LogiAI-Marmara/Grid-Up-Hackathon/modul-sim/README.md

# modul-sim — Sentetik Modül Veri Üreteci ve Modül Mantığı

Grid Up Hackathon — İZ A (Saha ve Veri Yolu) bileşeni.

Pano içine yerleştirilen izleme modülünün ölçüm döngüsünü, termal dizi matrisini,
sensör davranışını ve arıza mekanizmalarını sentetik olarak simüle eden CLI aracıdır.

---

## 1. Ne Üretir?

Modül simülatörü, panodaki donanımın üreteceği paketleri **Sözleşme ② (`modul_paketi.schema.json`)**
formatında üretir. Çıktı standart `stdout` akışına yazılır (ndjson veya json dizi), çalışma
istatistikleri ise `stderr`'e basılır:

- `modul_id`: `{saha}-{pano}-{modul}` hiyerarşik kimliği (örn. `TR041-P01-M1`)
- `zaman`: ISO 8601 UTC zaman damgası
- `olcumler`: `akim_l1`, `akim_l2`, `akim_l3`, `akim_notr`, `termal_maks`, `termal_ort` (her paket); `ortam_sicaklik`, `nem` (60 sn'de bir); `ark_olay` (olay olunca)
- `termal_ozet`: `maks`, `maks_konum`, `bolge_ort` (4 bölge)
- `termal_kare`: 32×24 = 768 elemanlı sıcaklık matrisi, her pakette (pakette 0,01 °C; toplama DB'de int16 0,1 °C)
- `modul_durum`: `besleme` (`sebeke`/`yedek`), `sinyal` (dBm), `yazilim_surumu`

---

## 2. Desteklenen 7 Arıza Senaryosu

Karar kaydı §7.6 ile tanımlı tüm arıza senaryoları simüle edilebilir:

| Senaryo Adı (`--senaryo`) | Belirti | Beklenen Anomali Tipi |
|---|---|---|
| `gevsek_klemens` | Akım sabitken tek noktada (klemens) aşırı ısınma | `sicak_nokta`, `akim_sicaklik_sapmasi` |
| `asiri_yuk` | Tüm faz akımları anma değerini aşar, genel pano sıcaklığı artar | `asiri_yuk`, `ortam_sicaklik_yuksek` |
| `faz_dengesizlik` | Fazlar arası akım farkı ve nötr akımı yükselir | `faz_dengesizligi` |
| `nem_yuksek` | Bağıl nem yükselir, çiğ noktasına yaklaşarak yoğuşma riski doğurur | `nem_yuksek` |
| `ark_olay` | Optik ark algılama kaydı (TVOC-2 Modbus trip sinyali) | `ark` |
| `sensor_ariza` | Sensör donması veya gürültülü okuma (`kalite: supheli/yok`) | `sensor_arizasi` |
| `modul_saglik` | Şebeke besleme kaybı (`yedek`), RF sinyal düşüşü, saat kayması | `modul_saglik` |

Senaryo listesini terminalden görüntülemek için:
```bash
python -m modul_sim --liste
```

---

## 3. Kurulum ve Çalıştırma

Repo kök dizininde veya `modul-sim/` dizininde:

```bash
# Bağımlılıkları yükleme
pip install -e modul-sim/

# Varsayılan normal çalışma (9 modül, 60 dk, ndjson)
python -m modul_sim

# Belirli bir arıza senaryosu ile üretim (ör. gevşek klemens)
python -m modul_sim --senaryo gevsek_klemens --modul 9 --sure 60 > veri.ndjson

# Toplama servisine doğrudan canlı borulama (pipeline)
python -m modul_sim --senaryo gevsek_klemens | while read -r paket; do
    curl -s -X POST http://localhost:8000/paket \
         -H "Content-Type: application/json" \
         -d "$paket"
done

# Sözleşme doğrulamasını zorunlu tutarak koşu
python -m modul_sim --dogrula --senaryo asiri_yuk
```

### Parametreler

- `--senaryo`: Arıza senaryosu seçimi (boş bırakılırsa normal sakin profil)
- `--modul N`: Simüle edilecek modül sayısı (Demo: 9, Yük testi: 100)
- `--sure DK`: Simülasyon penceresi uzunluğu (dakika)
- `--tohum N`: Rastgele sayı üreteci tohumu (deterministik tekrarlanabilirlik)
- `--baslangic ISO`: Simülasyon başlangıç zamanı (varsayılan: koşunun şu an bitmesini sağlayacak an)
- `--cikti`: `ndjson` (satır satır) veya `json` (tek dizi)
- `--dogrula`: Her paketi çıkışta `modul_paketi.schema.json` şemasına karşı doğrular
- `--senaryo-bas DK` / `--senaryo-sure DK`: senaryonun başlama anı ve rampa süresi (varsayılan: koşunun %35'inde başlar, %55'i boyunca tırmanır)
- `--senaryo-modul ID[,ID...]`: senaryoyu yalnız bu modüllere uygula, kalanlar temiz kalır
- `--senaryo-oran 0-1`: senaryoyu filonun bu kesrine uygula (tohumdan deterministik seçim), kalanlar temiz
- `--etiket PATH`: koşu bitince kör test **etiket dosyasını** yaz (İZ B formatı, `analiz/README.md` "Etiket dosyası formatı": `senaryolar[].baslangic / kritik_esik`, `temiz_moduller`, `kapsam`)
- `--sessiz`: stderr'e koşu özeti basma

### Kör test seti üretme

```bash
# 20 modül, 12 saat; modüllerin %30'unda gevşek klemens, kalan 14 modül temiz
python -m modul_sim --senaryo gevsek_klemens --modul 20 --sure 720 --senaryo-oran 0.3 --etiket etiket.json > kor.ndjson
```

Veri (`kor.ndjson`) veritabanına gider; `etiket.json` dedektör çıktısı dondurulana kadar üreticide kalır
(`analiz/README.md` "Kör test protokolü"). `kritik_esik` rampanın sonu, ark için ilk trip anı; etiketteki
senaryo adları İZ B sözlüğüyle (`faz_dengesizligi`, `nem_yukselmesi`, `ark_olayi`, `sensor_arizasi`) yazılır,
CLI adları değişmez.

---

## 4. Testler

```bash
pytest modul-sim/tests/
```

Tüm senaryoların veri üretimi, fizik motorunun ısı transferi kısıtları ve sözleşme uyumluluğu
otomatik testlerle doğrulanmaktadır.

İlgili tasarım dokümantasyonu: [`docs/track-a/07-yazilim-akis.md`](../docs/track-a/07-yazilim-akis.md)
