LogiAI-Marmara/Grid-Up-Hackathon/docs/track-a/07-yazilim-akis.md

# 7. Modül Yazılım Akış Diyagramı

**Teslimat karşılığı:** T3 (yazılım mimarisi — modül kısmı)
**Dayandığı kararlar:** §7.2 örnekleme sıklığı · §7.4 veri politikası
**Yöntem:** Bu diyagram **uydurulmamıştır** — `/modul-sim/modul_sim/modul.py` içindeki gerçek
firmware akışından türetilmiştir. Kod tarafı PR #1 ile teslim edilmiş, entegrasyon kararıyla
(17 Eyl, commit `3b83483`) güncellenmiştir.

> **Kapsam notu — mikrodenetleyici kodu (T3):** Brief T3 *"mikrodenetleyici üzerinde çalışan
> kaynak kodlar"* der. İki gerçekleme var: (1) `/modul-sim` (Python) — modül mantığı + 7 arıza
> senaryosu, gerçek toplama servisine karşı koşan **asıl** kod; bu doküman onun akışıdır. (2) [`/firmware`](../../firmware/README.md) — aynı dokuz
> adımın ESP32-S3-WROOM-1U-N8 için C++ karşılığı (PlatformIO, Arduino): pinler
> [3. doküman §3.1](03-pinout.md)'den, sabitler `ayar.py`'den, paket sözleşme ② `POST /paket`.
> **Derlenir (RAM %26, flash %28); fiziksel modül üretilmediği için (§1.4) donanımda doğrulanmadı.**
> CT ön ucu ve Modbus register sabitleri sahadaki cihaza göre ayarlanacak varsayımlardır. Firmware
> senaryo üretmez; kaynak-doğruluk sırası: bu doküman ↔ `modul.py` ↔ `main.cpp` (§7.8).

---

## 7.1 Ana akış

```mermaid
flowchart TD
    START(["UYAN<br/>(paket çevrimi başlar)"]) --> W["Dünyayı oku<br/>dış hava, yük profili<br/>(simülatörde; sahada fiziksel dünya)"]
    W --> A["AKIM OKU<br/>2 sn alt örnekleme<br/>→ 30 sn ortalaması<br/>L1 / L2 / L3 / nötr"]
    A --> D["KABİN HAVASI<br/>sıcaklık + iç bağıl nem"]
    D --> ARC["ARK SAYACI<br/>TVOC-2 trip sayacı<br/>(olay bazlı, periyot yok)"]
    ARC --> CLK["MODÜL SAATİ<br/>serbest çalışır → kayma<br/>zaman damgası üret"]
    CLK --> LP{"Düşük güç?<br/>(yedek besleme, kritik)"}
    LP -->|"Evet — termal ve<br/>ölçümler atlanır"| ASM
    LP -->|"Hayır"| FRAME["768 DEĞER OKU<br/>32×24 termal kare<br/>(6 sn'de bir 5 alt kare → ortalama)"]
    FRAME --> SUM["ÖZETLE<br/>maks + konumu + 4 bölge ort.<br/>(768 → 7 sayı; kare ort. ayrı satır)"]
    SUM --> ATTACH["TAM KAREYİ EKLE<br/>her çevrimde, koşulsuz<br/>(entegrasyon kararı madde 2)"]
    ATTACH --> ASM

    ASM["ÖLÇÜM SATIRLARINI KUR<br/>(sözleşme ① formatı)<br/>ark olayı varsa ark_olay satırı"]
    ASM --> CEVRE{"Ortam/nem çevrimi?<br/>(her 60 sn = 2 çevrimde bir)"}
    CEVRE -->|"Evet"| ENV["Ortam sıcaklık + nem ekle"]
    CEVRE -->|"Hayır"| HEALTH
    ENV --> HEALTH

    HEALTH["MODÜL SAĞLIĞI<br/>besleme (sebeke/yedek)<br/>sinyal dBm · yazılım sürümü"]
    HEALTH --> SEND(["GÖNDER<br/>paket → saha gateway'i"])
    SEND --> START

    classDef read fill:#e3f2fd,stroke:#1565c0,color:#000
    classDef dec fill:#fff9c4,stroke:#f9a825,color:#000
    classDef frame fill:#ffe0b2,stroke:#e65100,color:#000
    classDef out fill:#c8e6c9,stroke:#2e7d32,color:#000
    class W,A,D,ARC,CLK,ASM,ENV,HEALTH read
    class LP,CEVRE dec
    class FRAME,SUM,ATTACH frame
    class START,SEND out
```

---

## 7.2 Örnekleme takvimi (§7.2, koddan doğrulanmış)

| Ölçüm | Karar kaydı §7.2 | Koddaki değer | Kaynak |
|---|---|---|---|
| Paket | — | `paket_s=30` | `OrneklemeAyar` |
| Akım | 1–5 sn okunur, 10 sn ort. kaydedilir | `akim_okuma_s=2` alt örnek, **30 sn** ort. (paket penceresi) | `OrneklemeAyar`, `modul.py` adım 3 |
| Termal özet | 10–30 sn | `termal_s=30`; sensör `termal_okuma_s=6` sn'de bir okunur, 5 alt kare ortalanır | `OrneklemeAyar`, adım 7 |
| Termal tam kare | Sadece anomali anında | **Her pakette** (entegrasyon kararı madde 2) | `modul.py` adım 7 |
| Ortam sıcaklık / nem | 30–60 sn | `cevre_s=60` (2 çevrimde bir) | `OrneklemeAyar` |
| Ark | Olay bazlı, örnekleme yok | `ark_tetik` olayı | `modul.py` adım 5 |

**Paket temposu neden 30 sn:** Paket periyodu **akım ortalama penceresidir**: akım 2 sn'de bir
okunur, 15 alt örneğin ortalaması kaydedilir; paket başına bir kayıt, **hiçbir veri atılmaz.**
Termal çevrim paketle aynı süreye hizalandı ki her pakette özet + kare birlikte gitsin ve
merkezdeki dedektör (İZ B, 30 sn tarama) her taramada yeni bir kare bulsun. Karar kaydı §7.2'nin
*"10 sn"* ve *"10–30 sn"* değerleri bu hizalamadan önceki değerlerdir.

---

## 7.3 Eşik kontrolü — kaldırıldı (entegrasyon kararı madde 2)

**Eski tasarım (karar kaydı §7.4 satır 298–304):** normalde yalnız özet gider; modül üç bağımsız
tetikle (`maks_c` 65 °C, `delta_c` 14 °C, `kabin_delta_c` 22 °C) + ark geçersiz kılma + 60 sn hız
sınırıyla *"bu çevrimde tam kare eklensin mi"* kararını verir. Bu, §7.4 satır 304'ün *"modülün
anomaliyi kendi başına tanıyabilmesi"* şartının karşılığıydı.

**Bugünkü durum (kod):** `modul.py` adım 7 kareyi **her çevrimde koşulsuz** ekler; eşik fonksiyonu
(`_kare_gerekli`) koddan çıkarıldı. `EsikAyar` yapılandırma nesnesi **duruyor ama değerlendirilmiyor**:
politika geri istenirse tek noktadan takılsın diye ve merkezden modüle ayar gönderme kavramının
(§7.4 satır 304, T5) yeri belli olsun diye korunmuştur.

**Neden değişti**: *"Eski politikanın dayanağı ölçülmemişti."* Belgenin saydığı üç kazanım: (1) modül içi
eşik mantığı ortadan kalkar, varlık sebebi karenin ne zaman gönderileceğine karar vermekti;
(2) kanıt karesinin *"en yakını hangisi"* sorunu kalkar, her olay anının kendi karesi vardır
(`kanit.kare_id`, `analiz/README` 10–11); (3) geçmişe dönük yeniden tarama gerçekten mümkün olur,
eski politikada geçmiş veri o zamanki eşiğin gönderdikleriyle sınırlıydı. Uygulama: commit
`3b83483`, `toplama/migrations/004`.

**Maliyeti:** kare başına 768 × int16 = **1 536 B** (DB'de, `toplama/migrations/004`; JSONB olarak
tutulsaydı 100 modülde ~430 MB/gün olacağı için ikili biçime geçildi); tel üzerinde JSON ≈ 3–4 KB.
100 modül × 30 sn → **≈ 5 KB/sn** DB yazımı, ≈ 12 KB/sn HTTP. On-prem sunucu ve saha gateway'i için
önemsiz; §7.4 satır 302'deki *"bant genişliğini düşük tutar"* gerekçesi bu ölçekte belirleyici
değildir. Modül tarafında ek yük yok: kare zaten her çevrim okunuyordu.

**Modül hâlâ ne yapar:** 768 değeri yuvarlayıp özetler (maks, konum, 4 bölge ortalaması) ve
kareyle birlikte paketler. Özet, dedektörün ucuz ilk bakışı; kare, kanıt. İkisi de her pakette.
---

## 7.4 ⚠️ Kritik mimari sınır — modül hüküm VERMEZ

Bu, dokümanın en önemli ayrımıdır ve karıştırılırsa sistem yanlış anlatılmış olur:

| Karar | Kim verir | Nerede |
|---|---|---|
| *"Kaç derece?"* | Sensör | Pano içi |
| *"768'den özet çıkar, kareyle birlikte paketle"* | **ESP32** | Pano içi |
| **"Bu bir anomali mi? Hangi tip? Hangi seviye?"** | **Anomali motoru** | **On-prem sunucu** |
| *"Alarm gönderilsin mi, kime?"* | Alarm servisi | On-prem sunucu |

**Modülün ürettiği pakette `seviye` ve `tip` alanları YOKTUR.** Bu alanlar anomali motorunun
çıktısıdır (sözleşme ③). Modül yalnızca *"şüpheli bir şey var, kanıtı da gönderiyorum"* der.

**Tespit tek katmanda, merkezde.** Karar kaydı §7.4 satır 304 *"modülde basit eşik mantığı,
merkezde asıl dedektör"* diyordu; entegrasyon kararıyla modül tarafındaki eşik kalktı (§7.3),
asıl dedektör zaten merkezdeydi. Modül hiçbir hüküm vermez, kanıtı (kare) her pakette gönderir.

**Merkezden modüle ayar:** 100 sahayı gezmemek için gerekli olan bu kanal (§7.4 satır 304, T5)
kodda `OrneklemeAyar` / `EsikAyar` yapılandırma nesneleriyle temsil edilir; protokolü sözleşme
kapsamı dışındadır (§7.9).

---

## 7.5 Veri politikası — özet vs tam kare

| Durum | Gönderilen | Boyut |
|---|---|---|
| **Her paket (30 sn)** | `termal_ozet` (maks + konum (2) + 4 bölge ort. = 7 sayı) **+** `termal_kare` (768 değer) | JSON ≈ 3–4 KB; DB 1 536 B (int16, 0,1 °C) |
| **Düşük güç** (`dusuk_guc`) | Yalnız `modul_durum` (+ varsa `ark_olay`) | < 200 B |

**Eski gerekçe (§7.4 satır 302)** *"özet + olay bazlı tam kare bant genişliğini düşük tutar"*
entegrasyon kararıyla terk edildi; sayısal karşılığı §7.3'te (100 modül ≈ 5 KB/sn). *"Edge'de
işlem"* iddiasının bugünkü karşılığı **özet çıkarma + düşük güç modu**dur, kare seçimi değil.

**Özetin içeriği (sözleşme ② ile birebir):**

| Alan | İçerik |
|---|---|
| `maks` | Karenin en sıcak pikseli (°C) |
| `maks_konum` | `[sütun, satır]` — örn. `[14, 9]` |
| `bolge_ort` | 4 × 16×12 çeyrek bölgenin ortalaması: sol-üst, sağ-üst, sol-alt, sağ-alt |

**Kritik uygulama detayı (koddan):** Özet, **karenin gönderildiği hali üzerinden** hesaplanır —
yuvarlama özetten **önce** yapılır. Sebep: toplayıcı, `maks_konum`'un gerçekten aldığı karenin en
sıcak pikselini işaret ettiğini doğrular. Yuvarlama sırası karışırsa bu kontrol tutmaz.

---

## 7.6 Modül sağlığı — "sessizce ölmeme" kanalı

Her pakette `modul_durum` gönderilir:

| Alan | Değerler | Rolü |
|---|---|---|
| `besleme` | `sebeke` / `yedek` | **`yedek` geçişi = besleme kaybı alarmı.** Süperkapasitörün var olma sebebi budur (§7.3 satır 269) |
| `sinyal` | dBm (negatif) | Zayıflama eğilimi, kararmak üzere olan modül için erken uyarı |
| `yazilim_surumu` | semver | Sürüm takibi |

**Ek davranış (koddan):** Yedek beslemeye geçildiğinde verici **düşük güçte** çalışır ve sinyal
değeri 4 dBm zayıflatılır — enerji tasarrufu. Süperkapasitör kritik seviyeye inince (`dusuk_guc`)
modül termal diziyi ve ölçüm satırlarını **tamamen atlar**; yalnız `modul_durum` (ve varsa ark olayı)
gönderilir — *"termal dizi ile radyo aynı anda karşılanamaz, modül ölmekte olduğunu söyleyen kalp
atışı dışında her şeyi bırakır"* (`senaryo.py`). Diyagramdaki **Düşük güç?** dalı budur.

**Kalite alanı:** Sensör arızası senaryosunda (`sensor_arizasi`) ölçüm değeri ya `null` olur ve
`kalite: yok` işaretlenir, ya da mantıksız bir değer `kalite: supheli` ile işaretlenir. Kural:
**yalnız `kalite: yok` null değer taşıyabilir** — bu kural şemada, veritabanı CHECK kısıtında ve
kodda üç yerde birden uygulanır.

---

## 7.7 Saat davranışı

**Modülün saati serbest çalışır** ve sağlıklıyken bile az miktarda kayar (senaryo 7'nin bir
bileşeni). Toplayıcı bu kaymayı **`alindi_zaman` − `zaman`** farkı olarak görür.

**Sözleşme kuralı (§11):** Modül `zaman` atar, toplayıcı `alindi_zaman` ekler. Zaman biçimi UTC
ISO 8601, **literal `Z`** ile — `+03:00` gibi offset'ler reddedilir. Gerekçe: tek saat dilimi
kullanmak, demoda *"bu yerel saat mi UTC mi"* sorusunu tamamen ortadan kaldırır.

---

## 7.8 Akışın kodla eşleşmesi (doğrulama)

| Diyagram adımı | Simülatör (`modul-sim/modul_sim/modul.py`) | Firmware (`firmware/src/main.cpp`) |
|---|---|---|
| Dünyayı oku | adım 1 — `hava.ilerle()`, `Baglam` | sahada fiziksel; sensör okumasının içinde |
| Senaryo uygula | adım 2 — `senaryo.uygula()` | yok (senaryo simülatörün işi) |
| Akım oku (2 sn → 30 sn ort.) | adım 3 — `alt_adim` döngüsü | `akimOku()` × 15: `ctRmsAmper()` (ADC1) veya Modbus analizör |
| Kabin havası | adım 4 — `_kabin.ilerle()`, `ic_bagil_nem()` | `Adafruit_SHT31` sıcaklık + nem |
| Ark sayacı | adım 5 — `ark_tetik` | `arkTetikOku()`: TVOC-2 trip register farkı |
| Modül saati | adım 6 — `saat_kayma_ppm` | SNTP → `zamanYaz()`; saat yoksa paket atlanır |
| Düşük güç? | `b.dusuk_guc` — adım 7 ve 8'i atlar | yedekte ≥ 3 dk (`YEDEK_DUSUK_GUC_S`) — aynı atlama |
| Termal oku + özetle + kareyi ekle | adım 7 — `dizi.kare()` × 5 alt kare, `TermalDizi.ozet()`, `termal_kare = kare` | `termalAltKareEkle()` × 5, `termalKareBitir()` (yuvarla → maks, konum, 4 bölge) |
| Ölçüm satırlarını kur | adım 8 | `olcumSatiri()`, yalnız `kalite: yok` `null` |
| Modül sağlığı | adım 9 — `modul_durum` | VSENSE → `besleme`, `WiFi.RSSI()` → `sinyal` |
| Gönder | `UretilenPaket` döner | `HTTPClient.POST(TOPLAMA_URL)` |

**Doğrulama:** Diyagramdaki dokuz adım, `ilerle()` fonksiyonundaki dokuz numaralı adımla ve
`main.cpp`'deki `loop()` yorumlarıyla **birebir** eşleşir. Sabitler tek yerden gelir
(`ayar.py` ↔ `firmware/include/ayar.h`). Simülatör test edilmiştir (39 test); firmware yalnız derlenmiştir.

---

## 7.9 Kapsam dışı

| Konu | Nerede |
|---|---|
| Toplama servisi (paket alma, doğrulama, DB yazma) | `/toplama` — İZ A kod tarafı |
| Anomali motoru ve dedektörler | İZ B |
| Seviye/tip kararı, alarm kuralları | İZ B, İZ C |
| Merkezden modüle ayar gönderme protokolü | Tasarım gereği gerekli (§7.4); sözleşme kapsamı dışında, gelecek çalışma |
| Arayüz, Modbus sunucusu | İZ C |
