LogiAI-Marmara/Grid-Up-Hackathon/docs/track-a/eda/GridUp-Modul.kicad_sch

## KiCad design docs/track-a/eda/GridUp-Modul.kicad_sch (2026-09-18)

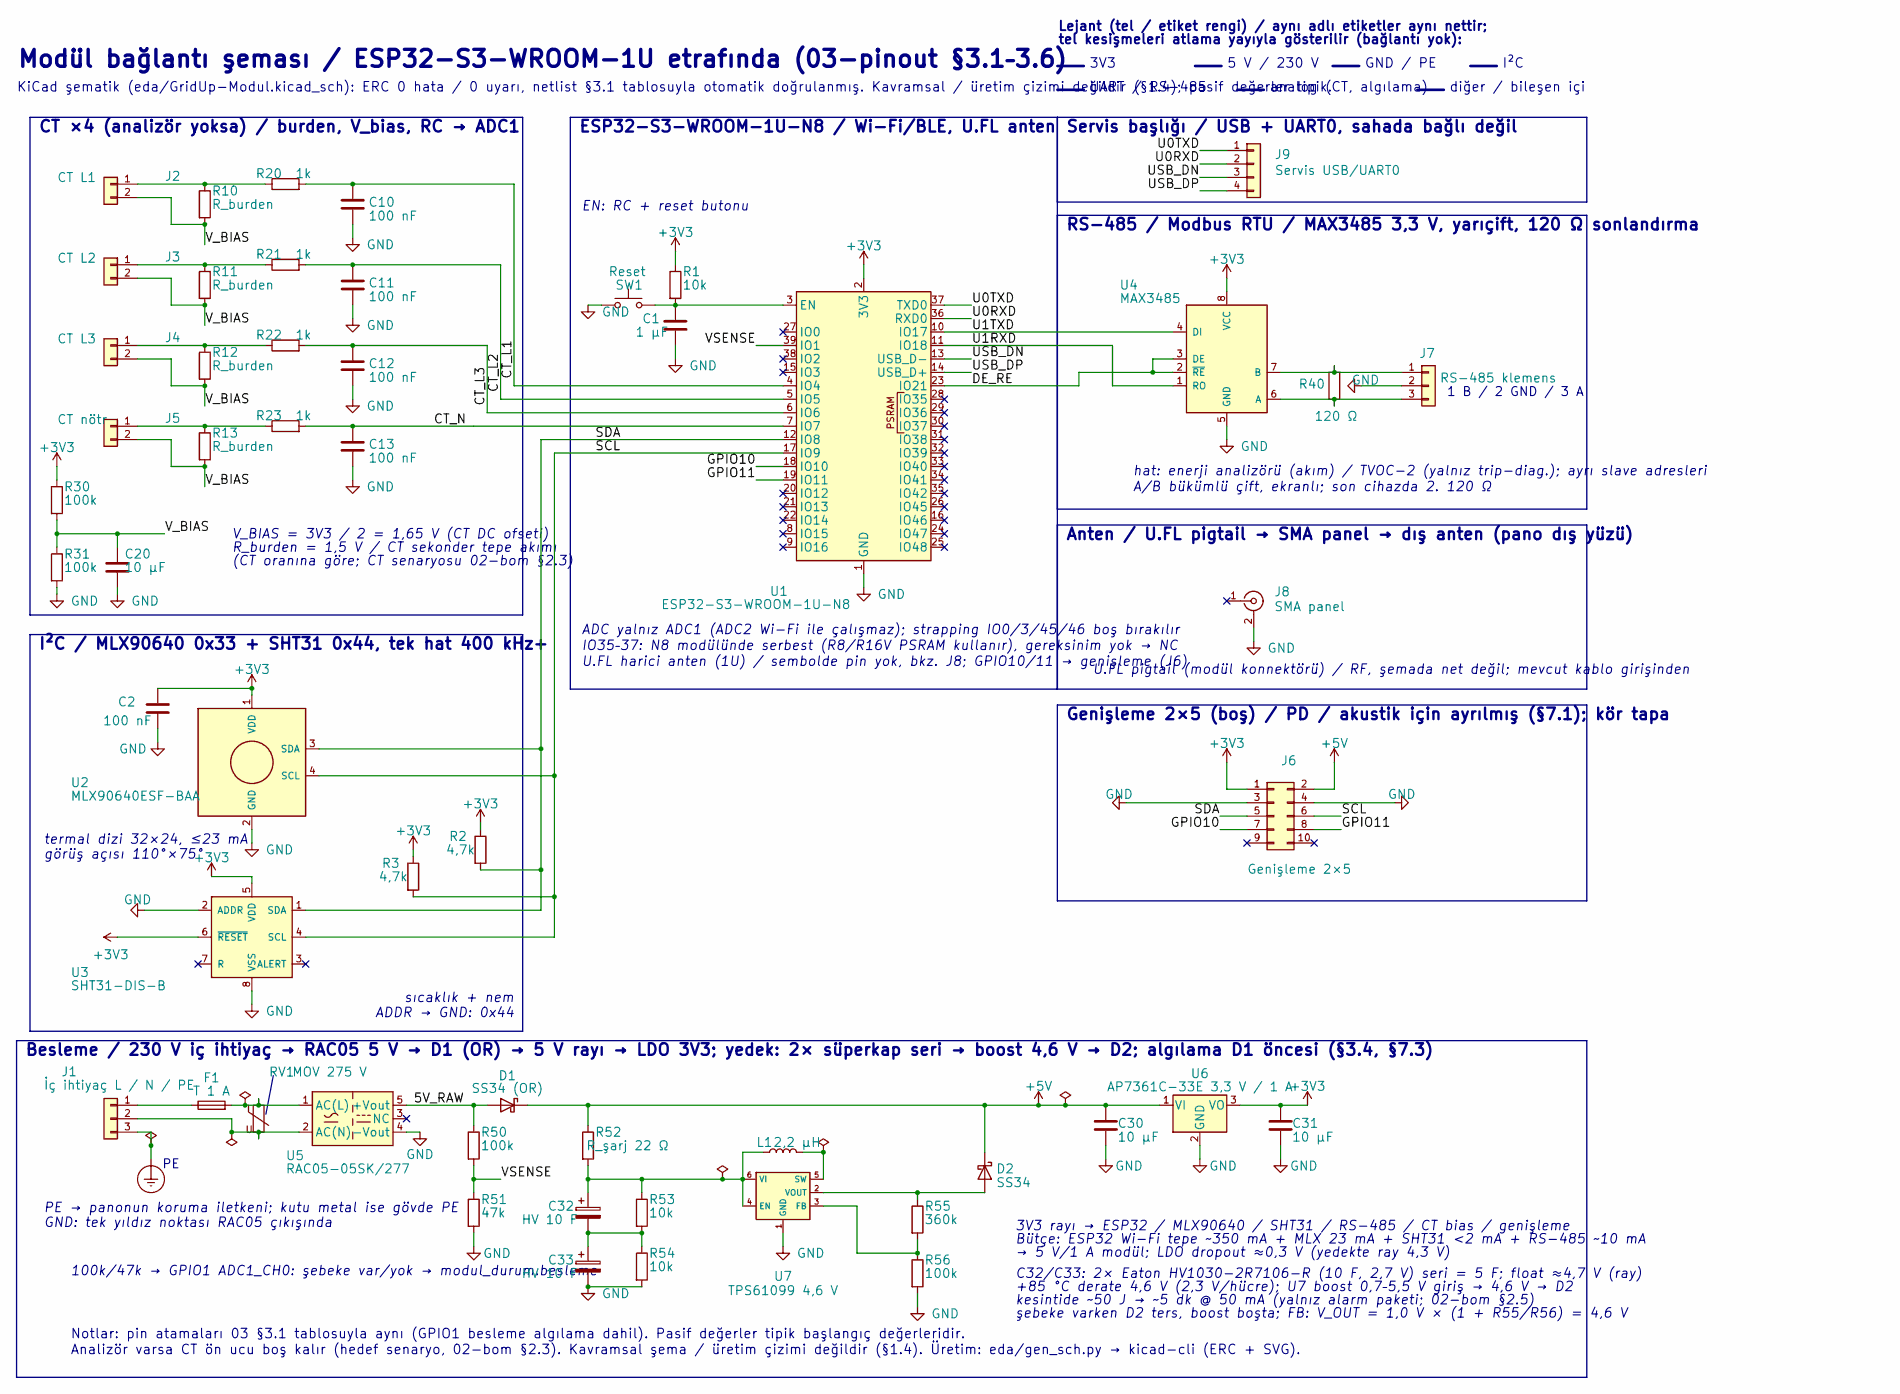
[picture p5: schematic GridUp-Modul.kicad_sch]

Parts:
C1: 1 µF
C2, C10, C11, C12, C13: 100 nF
C20, C30, C31: 10 µF
C32, C33: HV 10 F
D1: SS34 (OR)
D2: SS34
F1: T 1 A
J1: İç ihtiyaç L / N / PE; TerminalBlock_Phoenix_MKDS-3-3-5.08_1x03_P5.08mm_Horizontal
J2: CT L1; TerminalBlock_Phoenix_MKDS-3-2-5.08_1x02_P5.08mm_Horizontal
J3: CT L2; TerminalBlock_Phoenix_MKDS-3-2-5.08_1x02_P5.08mm_Horizontal
J4: CT L3; TerminalBlock_Phoenix_MKDS-3-2-5.08_1x02_P5.08mm_Horizontal
J5: CT nötr; TerminalBlock_Phoenix_MKDS-3-2-5.08_1x02_P5.08mm_Horizontal
J6: Genişleme 2×5; PinHeader_2x05_P2.54mm_Vertical
J7: RS-485 klemens; TerminalBlock_Phoenix_MKDS-3-3-5.08_1x03_P5.08mm_Horizontal
J8: SMA panel; SMA_Amphenol_132134_Vertical
J9: Servis USB/UART0; PinHeader_1x04_P2.54mm_Vertical
L1: 2,2 µH
R1, R53, R54: 10k
R2, R3: 4,7k
R10, R11, R12, R13: R_burden
R20, R21, R22, R23: 1k
R30, R31, R50, R56: 100k
R40: 120 Ω
R51: 47k
R52: R_şarj 22 Ω
R55: 360k
RV1: MOV 275 V
SW1: Reset
U1: ESP32-S3-WROOM-1U-N8; ESP32-S3-WROOM-1U
U2: MLX90640ESF-BAA; TO-39-4
U3: SHT31-DIS-B; Sensirion_DFN-8-1EP_2.5x2.5mm_P0.5mm_EP1.1x1.7mm
U4: MAX3485; SOIC-8_3.9x4.9mm_P1.27mm
U5: RAC05-05SK/277; Converter_ACDC_RECOM_RAC05-xxSK_THT
U6: AP7361C-33E 3,3 V / 1 A; SOT-223-3_TabPin2
U7: TPS61099 4,6 V; WSON-6-1EP_2x2mm_P0.65mm_EP1x1.6mm

Connections:
5V_RAW: D1.2 (A), R50.1, U5.5 (+Vout)
+3V3: C2.1, C31.1, J6.1, R1.1, R2.1, R3.1, R30.1, U1.2 (3V3), U2.1 (VDD), U3.5 (VDD), U3.6 (~RESET), U4.8 (VCC), U6.3 (VO)
+5V: C30.1, D1.1 (K), D2.1 (K), J6.2, R52.1, U6.1 (VI)
CT_L1: C10.1, R20.2, U1.4 (IO4)
CT_L2: C11.1, R21.2, U1.5 (IO5)
CT_L3: C12.1, R22.2, U1.6 (IO6)
CT_N: C13.1, R23.2, U1.7 (IO7)
DE_RE: U1.23 (IO21), U4.2 (~RE), U4.3 (DE)
Earth_Protective: J1.3
GND: C1.2, C2.2, C10.2, C11.2, C12.2, C13.2, C20.2, C30.2, C31.2, C33.2, J6.3, J6.4, J7.2, J8.2 (Ext), R31.2, R51.2, R54.2, R56.2, SW1.1, U1.1 (GND), U1.40 (GND), U1.41 (GND), U2.2 (GND), U3.2 (ADDR), U3.8 (VSS), U4.5 (GND), U5.4 (-Vout), U6.2 (GND), U7.1 (GND), U7.7 (GND)
GPIO10: J6.7, U1.18 (IO10)
GPIO11: J6.8, U1.19 (IO11)
unnamed: C1.1, R1.2, SW1.2, U1.3 (EN)
unnamed: C32.1, L1.1, R52.2, R53.1, U7.4 (EN), U7.6 (VI)
unnamed: C32.2, C33.1, R53.2, R54.1
unnamed: D2.2 (A), R55.1, U7.2 (VOUT)
unnamed: F1.1, J1.1
unnamed: F1.2, RV1.1, U5.1 (AC(L))
unnamed: J1.2, RV1.2, U5.2 (AC(N))
unnamed: J2.1, R10.1, R20.1
unnamed: J3.1, R11.1, R21.1
unnamed: J4.1, R12.1, R22.1
unnamed: J5.1, R13.1, R23.1
unnamed: J7.1, R40.1, U4.7 (B)
unnamed: J7.3, R40.2, U4.6 (A)
unnamed: L1.2, U7.5 (SW)
unnamed: R55.2, R56.1, U7.3 (FB)
SCL: J6.6, R3.2, U1.17 (IO9), U2.4 (SCL), U3.4 (SCL)
SDA: J6.5, R2.2, U1.12 (IO8), U2.3 (SDA), U3.1 (SDA)
U0RXD: J9.2, U1.36 (RXD0)
U0TXD: J9.1, U1.37 (TXD0)
U1RXD: U1.11 (IO18), U4.1 (RO)
U1TXD: U1.10 (IO17), U4.4 (DI)
USB_DN: J9.3, U1.13 (USB_D-)
USB_DP: J9.4, U1.14 (USB_D+)
VSENSE: R50.2, R51.1, U1.39 (IO1)
V_BIAS: C20.1, J2.2, J3.2, J4.2, J5.2, R10.2, R11.2, R12.2, R13.2, R30.2, R31.1

Notes on the sheet:
Modül bağlantı şeması / ESP32-S3-WROOM-1U etrafında (03-pinout §3.1–3.6)
KiCad şematik (eda/GridUp-Modul.kicad_sch): ERC 0 hata / 0 uyarı, netlist §3.1 tablosuyla otomatik doğrulanmış. Kavramsal / üretim çizimi değildir (§1.4); pasif değerler tipik.
Lejant (tel / etiket rengi) / aynı adlı etiketler aynı nettir;
tel kesişmeleri atlama yayıyla gösterilir (bağlantı yok):
3V3
5 V / 230 V
GND / PE
I²C
UART / RS-485
analog (CT, algılama)
diğer / bileşen içi
ESP32-S3-WROOM-1U-N8 / Wi-Fi/BLE, U.FL anten
ADC yalnız ADC1 (ADC2 Wi-Fi ile çalışmaz); strapping IO0/3/45/46 boş bırakılır
IO35–37: N8 modülünde serbest (R8/R16V PSRAM kullanır), gereksinim yok → NC
U.FL harici anten (1U) / sembolde pin yok, bkz. J8; GPIO10/11 → genişleme (J6)
EN: RC + reset butonu
CT ×4 (analizör yoksa) / burden, V_bias, RC → ADC1
V_BIAS = 3V3 / 2 = 1,65 V (CT DC ofseti)
R_burden = 1,5 V / CT sekonder tepe akımı
(CT oranına göre; CT senaryosu 02-bom §2.3)
I²C / MLX90640 0x33 + SHT31 0x44, tek hat 400 kHz+
termal dizi 32×24, ≤23 mA
görüş açısı 110°×75°
sıcaklık + nem
ADDR → GND: 0x44
Servis başlığı / USB + UART0, sahada bağlı değil
RS-485 / Modbus RTU / MAX3485 3,3 V, yarıçift, 120 Ω sonlandırma
1 B / 2 GND / 3 A
hat: enerji analizörü (akım) / TVOC-2 (yalnız trip-diag.); ayrı slave adresleri
A/B bükümlü çift, ekranlı; son cihazda 2. 120 Ω
Anten / U.FL pigtail → SMA panel → dış anten (pano dış yüzü)
U.FL pigtail (modül konnektörü) / RF, şemada net değil; mevcut kablo girişinden
Genişleme 2×5 (boş) / PD / akustik için ayrılmış (§7.1); kör tapa
Besleme / 230 V iç ihtiyaç → RAC05 5 V → D1 (OR) → 5 V rayı → LDO 3V3; yedek: 2× süperkap seri → boost 4,6 V → D2; algılama D1 öncesi (§3.4, §7.3)
PE → panonun koruma iletkeni; kutu metal ise gövde PE
GND: tek yıldız noktası RAC05 çıkışında
100k/47k → GPIO1 ADC1_CH0: şebeke var/yok → modul_durum.besleme
3V3 rayı → ESP32 / MLX90640 / SHT31 / RS-485 / CT bias / genişleme
Bütçe: ESP32 Wi-Fi tepe ~350 mA + MLX 23 mA + SHT31 <2 mA + RS-485 ~10 mA
→ 5 V/1 A modül; LDO dropout ≈0,3 V (yedekte ray 4,3 V)
C32/C33: 2× Eaton HV1030-2R7106-R (10 F, 2,7 V) seri = 5 F; float ≈4,7 V (ray)
+85 °C derate 4,6 V (2,3 V/hücre); U7 boost 0,7–5,5 V giriş → 4,6 V → D2
kesintide ~50 J → ~5 dk @ 50 mA (yalnız alarm paketi; 02-bom §2.5)
şebeke varken D2 ters, boost boşta; FB: V_OUT = 1,0 V × (1 + R55/R56) = 4,6 V
Notlar: pin atamaları 03 §3.1 tablosuyla aynı (GPIO1 besleme algılama dahil). Pasif değerler tipik başlangıç değerleridir.
Analizör varsa CT ön ucu boş kalır (hedef senaryo, 02-bom §2.3). Kavramsal şema / üretim çizimi değildir (§1.4). Üretim: eda/gen_sch.py → kicad-cli (ERC + SVG).
